krishpr0/CONTROLLEr/PICTURES/_PCB_v1_2026-Jun-18_11-57-01AM-000_CustomizedView5992248504-removebg-preview.png

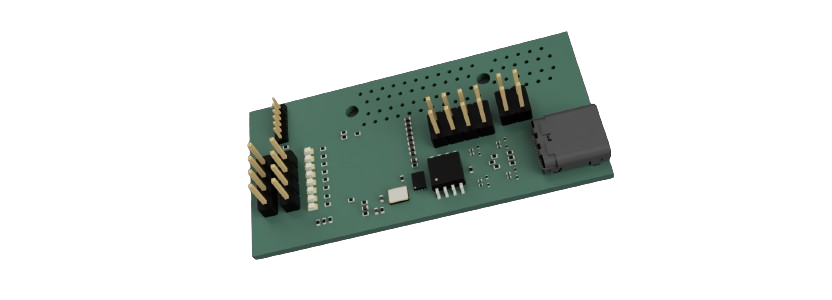
PICTURES/_PCB_v1_2026-Jun-18_11-57-01AM-000_CustomizedView5992248504-removebg-preview.png
