krishpr0/CONTROLLEr/PICTURES/_PCB_v1_2026-Jun-18_11-57-20AM-000_CustomizedView27303303591-removebg-preview.png

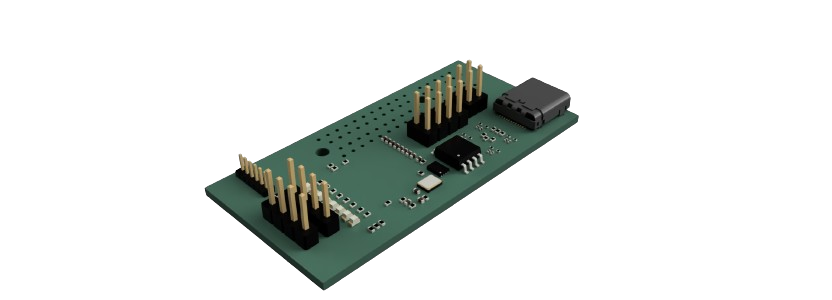
PICTURES/_PCB_v1_2026-Jun-18_11-57-20AM-000_CustomizedView27303303591-removebg-preview.png
