krishpr0/CONTROLLEr/PICTURES/_PCB_v54-removebg-preview.png

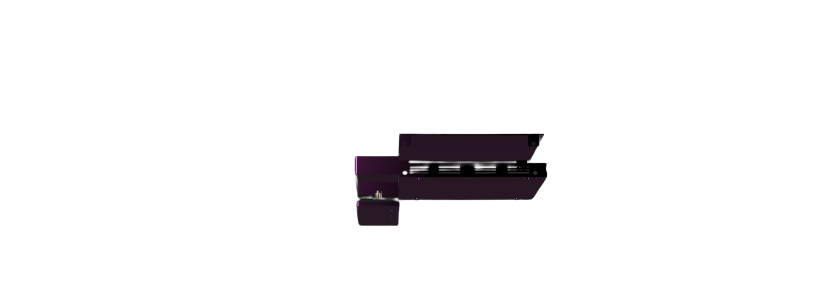
PICTURES/_PCB_v54-removebg-preview.png
