krishpr0/CONTROLLEr/PICTURES/CASE.png

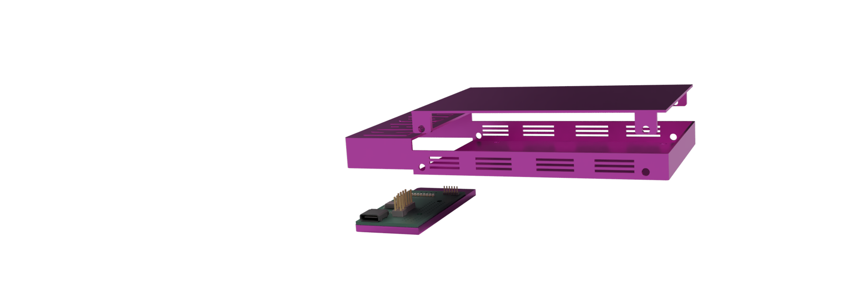
PICTURES/CASE.png
