krishpr0/CONTROLLEr/PICTURES/{PCB v46.png

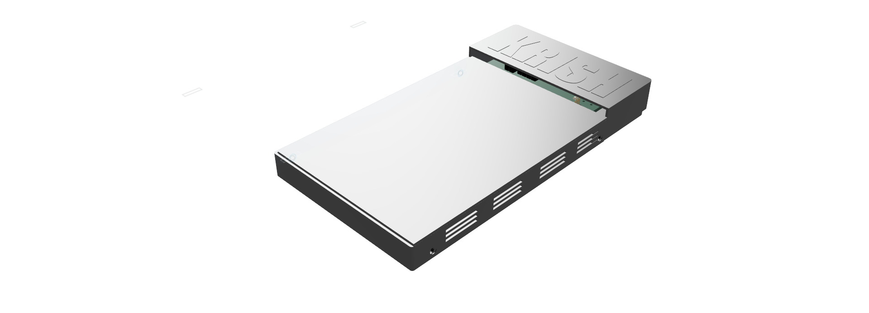
PICTURES/{PCB v46.png
