krishpr0/CONTROLLEr/PICTURES/{PCB v48.png

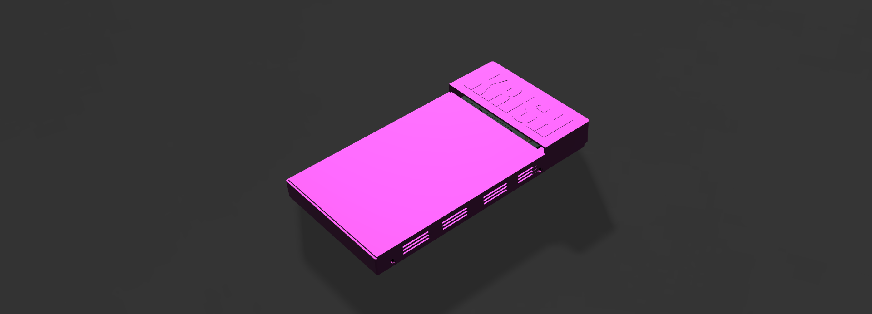
PICTURES/{PCB v48.png
