krishpr0/CONTROLLEr/PICTURES/{PCB v54.png

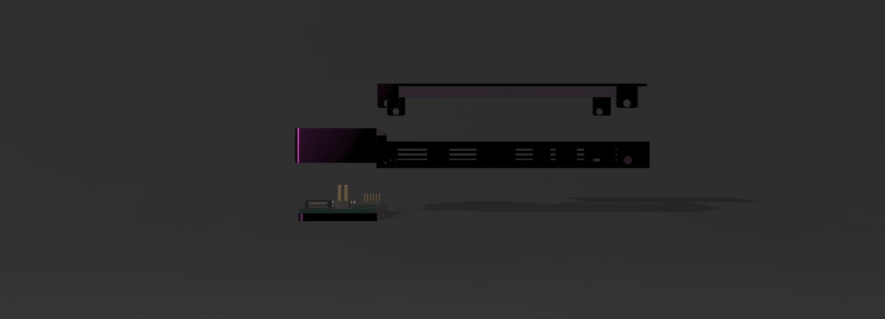
PICTURES/{PCB v54.png
