krishpr0/CONTROLLEr/PICTURES/{PCB_v1_2026-Jun-18_01-25-00PM-000_CustomizedView19356316654.png

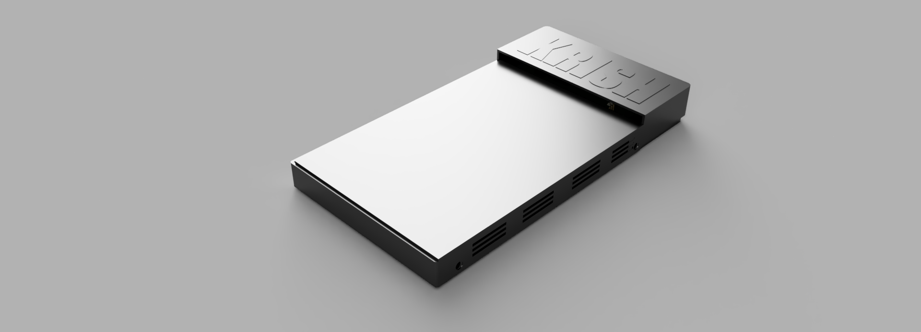
PICTURES/{PCB_v1_2026-Jun-18_01-25-00PM-000_CustomizedView19356316654.png
