krishpr0/CONTROLLEr/PICTURES/{PCB_v1_2026-Jun-18_04-54-52PM-000_CustomizedView25151271688.png

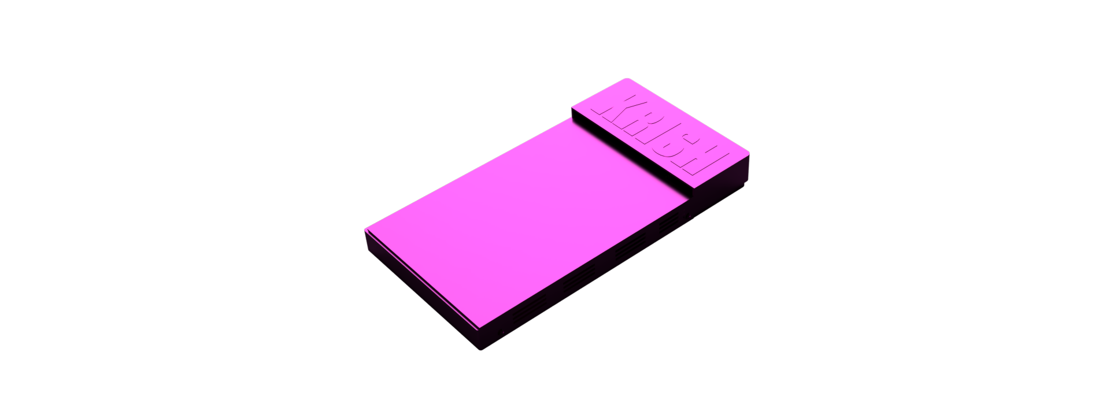
PICTURES/{PCB_v1_2026-Jun-18_04-54-52PM-000_CustomizedView25151271688.png
