krishpr0/CONTROLLEr/ZINE.png

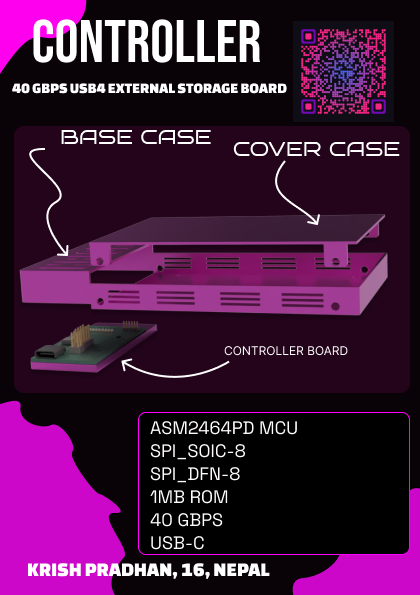
ZINE.png
