krishpr0/CONTROLLEr/FIRMWARE/src/src/app/buffer.c

/*
 * ASM2464PD Firmware - Buffer Controller Driver
 *
 * Handles buffer control, configuration, and data transfer management.
 * The buffer controller manages data movement between USB endpoints,
 * PCIe/NVMe, and internal memory.
 *
 *===========================================================================
 * BUFFER CONTROLLER ARCHITECTURE
 *===========================================================================
 *
 * Hardware Configuration:
 * - Internal data buffer for USB/PCIe transfers
 * - Configurable transfer modes and directions
 * - Status registers for tracking transfer progress
 *
 * Register Map (0xD800-0xD80F):
 * +-----------+----------------------------------------------------------+
 * | Address   | Description                                              |
 * +-----------+----------------------------------------------------------+
 * | 0xD800    | Buffer control (mode select: 0x03, 0x04)                 |
 * | 0xD801    | Buffer select                                            |
 * | 0xD802    | Buffer data/pointer                                      |
 * | 0xD803    | Pointer low                                              |
 * | 0xD804    | Pointer high / config from 0x911F                        |
 * | 0xD805    | Length low / config from 0x9120                          |
 * | 0xD806    | Status / config from 0x9121                              |
 * | 0xD807    | Length high / config from 0x9122                         |
 * | 0xD808    | Control global / params from idata[0x72]                 |
 * | 0xD809    | Threshold high / params from idata[0x71]                 |
 * | 0xD80A    | Threshold low / params from idata[0x70]                  |
 * | 0xD80B    | Flow control / params from idata[0x6f]                   |
 * | 0xD80C    | Transfer start (0x01=mode1, 0x02=mode2)                  |
 * +-----------+----------------------------------------------------------+
 *
 * Transfer Modes:
 * - Mode 0x03: Standard data transfer configuration
 * - Mode 0x04: Extended/special transfer configuration
 * - Transfer Start 0x01: Mode 1 transfer (USB/endpoint related)
 * - Transfer Start 0x02: Mode 2 transfer (PCIe/NVMe related)
 *
 * State Machine (idata[0x6a]):
 * - State 0x01: Idle/ready
 * - State 0x02: Transfer pending
 * - State 0x03: Transfer in progress
 * - State 0x04: Transfer complete
 * - State 0x05: Post-transfer processing
 * - State 0x08: Error/timeout
 *
 *===========================================================================
 * IMPLEMENTATION STATUS
 *===========================================================================
 * buf_set_ctrl_mode_4         [DONE] Set buffer to mode 0x04
 * buf_set_ctrl_mode_3         [DONE] Set buffer to mode 0x03
 * buf_write_idata_params      [DONE] Write idata params to buffer regs
 * buf_config_from_status      [DONE] Copy status regs to buffer config
 * buf_start_xfer_mode1        [DONE] Start mode 1 transfer
 * buf_start_xfer_mode2        [DONE] Start mode 2 transfer
 * buf_check_transfer_pending  [DONE] Check if transfer is pending
 *
 * Total: 7 functions implemented
 *===========================================================================
 */

#include "types.h"
#include "sfr.h"
#include "registers.h"
#include "globals.h"
#include "structs.h"

/*
 * buf_set_ctrl_mode_4 - Set buffer control to mode 0x04
 * Address: 0x025a-0x0269
 *
 * Configures the buffer for mode 0x04 operation and sets up
 * the length high register from xdata[0x0054].
 *
 * Original disassembly:
 *   025a: mov dptr, #0xd800   ; Buffer control
 *   025d: mov a, #0x04        ; Mode 4
 *   025f: movx @dptr, a       ; Write mode
 *   0260: mov dptr, #0x0054   ; Source address
 *   0263: movx a, @dptr       ; Read value
 *   0264: mov dptr, #0xd807   ; Length high
 *   0267: movx @dptr, a       ; Write length high
 *   0268: mov r4, #0x08       ; Return value in r4
 *   026a: sjmp 0x02c4         ; Continue...
 */
void buf_set_ctrl_mode_4(void)
{
    USB_BUF_CTRL->ctrl = 0x04;
    USB_BUF_CTRL->length_high = G_BUFFER_LENGTH_HIGH;
}

/*
 * buf_set_ctrl_mode_3 - Set buffer control to mode 0x03
 * Address: 0x026c-0x0271
 *
 * Configures the buffer for mode 0x03 operation.
 *
 * Original disassembly:
 *   026c: mov dptr, #0xd800   ; Buffer control
 *   026f: mov a, #0x03        ; Mode 3
 *   0271: movx @dptr, a       ; Write mode
 */
void buf_set_ctrl_mode_3(void)
{
    USB_BUF_CTRL->ctrl = 0x03;
}

/*
 * buf_write_idata_params - Write idata parameters to buffer registers
 * Address: 0x53c0-0x53d3
 *
 * Copies 4 bytes from idata[0x6f-0x72] to buffer registers 0xD808-0xD80B.
 * The bytes are written in reverse order (0x72->D808, 0x71->D809, etc).
 *
 * Original disassembly:
 *   53c0: mov r0, #0x72       ; Start at idata 0x72
 *   53c2: mov a, @r0          ; Read idata[0x72]
 *   53c3: mov dptr, #0xd808   ; Buffer control global
 *   53c6: movx @dptr, a       ; Write to D808
 *   53c7: dec r0              ; r0 = 0x71
 *   53c8: mov a, @r0          ; Read idata[0x71]
 *   53c9: inc dptr            ; dptr = 0xD809
 *   53ca: movx @dptr, a       ; Write to D809
 *   53cb: dec r0              ; r0 = 0x70
 *   53cc: mov a, @r0          ; Read idata[0x70]
 *   53cd: inc dptr            ; dptr = 0xD80A
 *   53ce: movx @dptr, a       ; Write to D80A
 *   53cf: dec r0              ; r0 = 0x6f
 *   53d0: mov a, @r0          ; Read idata[0x6f]
 *   53d1: inc dptr            ; dptr = 0xD80B
 *   53d2: movx @dptr, a       ; Write to D80B
 *   53d3: ret
 */
void buf_write_idata_params(void)
{
    /*
     * Note: This function uses idata (internal RAM) at addresses 0x6f-0x72.
     * In 8051, idata is accessed via indirect addressing with R0/R1.
     * These are internal state bytes for buffer configuration.
     */
    USB_BUF_CTRL->ctrl_global = I_BUF_CTRL_GLOBAL;   /* idata[0x72] -> 0xD808 */
    USB_BUF_CTRL->threshold_high = I_BUF_THRESH_HI;  /* idata[0x71] -> 0xD809 */
    USB_BUF_CTRL->threshold_low = I_BUF_THRESH_LO;   /* idata[0x70] -> 0xD80A */
    USB_BUF_CTRL->flow_ctrl = I_BUF_FLOW_CTRL;       /* idata[0x6f] -> 0xD80B */
}

/*
 * buf_config_from_status - Configure buffer from status registers
 * Address: 0x3147-0x3167
 *
 * Copies configuration from status registers 0x911F-0x9122 to
 * buffer registers 0xD804-0xD807.
 *
 * Original disassembly:
 *   3147: mov dptr, #0x911f   ; Status source
 *   314a: movx a, @dptr       ; Read 0x911F
 *   314b: mov dptr, #0xd804   ; Buffer ptr high
 *   314e: movx @dptr, a       ; Write to D804
 *   314f: mov dptr, #0x9120   ; Status source
 *   3152: movx a, @dptr       ; Read 0x9120
 *   3153: mov dptr, #0xd805   ; Buffer length low
 *   3156: movx @dptr, a       ; Write to D805
 *   3157: mov dptr, #0x9121   ; Status source
 *   315a: movx a, @dptr       ; Read 0x9121
 *   315b: mov dptr, #0xd806   ; Buffer status
 *   315e: movx @dptr, a       ; Write to D806
 *   315f: mov dptr, #0x9122   ; Status source
 *   3162: movx a, @dptr       ; Read 0x9122
 *   3163: mov dptr, #0xd807   ; Buffer length high
 *   3166: movx @dptr, a       ; Write to D807
 *   3167: ret
 */
void buf_config_from_status(void)
{
    USB_BUF_CTRL->ptr_high = REG_CBW_TAG_0;
    USB_BUF_CTRL->length_low = REG_CBW_TAG_1;
    USB_BUF_CTRL->status = REG_CBW_TAG_2;
    USB_BUF_CTRL->length_high = REG_CBW_TAG_3;
}

/*
 * buf_start_xfer_mode1 - Start buffer transfer in mode 1
 * Address: 0x5256-0x525f
 *
 * Initiates a mode 1 buffer transfer by writing 0x01 to the
 * transfer start register, then calls the transfer handler.
 *
 * Original disassembly:
 *   5256: mov dptr, #0xd80c   ; Transfer start reg
 *   5259: mov a, #0x01        ; Mode 1
 *   525b: movx @dptr, a       ; Start transfer
 *   525c: lcall 0x1bcb        ; Call transfer handler
 *   525f: ret
 */
void buf_start_xfer_mode1(void)
{
    USB_BUF_CTRL->xfer_start = 0x01;
    /* Note: Original calls 0x1bcb which is a transfer handler
     * that processes the buffer state machine. The actual
     * transfer handler would need to be called here. */
}

/*
 * buf_start_xfer_mode2 - Start buffer transfer in mode 2
 * Address: 0x018b-0x0198
 *
 * Initiates a mode 2 buffer transfer by writing 0x02 to the
 * transfer start register, calls the transfer handler, and
 * sets the state machine to state 0x05.
 *
 * Original disassembly:
 *   018b: mov dptr, #0xd80c   ; Transfer start reg
 *   018e: mov a, #0x02        ; Mode 2
 *   0190: movx @dptr, a       ; Start transfer
 *   0191: lcall 0x01ea        ; Call helper (writes idata params)
 *   0194: mov r0, #0x6a       ; State variable address
 *   0196: mov @r0, #0x05      ; Set state to 5
 *   0198: ret
 */
void buf_start_xfer_mode2(void)
{
    __idata uint8_t *state_ptr = (__idata uint8_t *)0x6a;

    USB_BUF_CTRL->xfer_start = 0x02;
    /* Note: Original calls 0x01ea which calls buf_write_idata_params
     * and then sets a register. For now we just set the state. */
    buf_write_idata_params();
    *state_ptr = 0x05;
}

/*
 * buf_check_transfer_pending - Check if a transfer operation is pending
 * Address: 0x313d-0x3146
 *
 * Reads 4 bytes from idata[0x6b-0x6e] and returns non-zero if any
 * are set, indicating a pending transfer operation.
 *
 * Original disassembly:
 *   313d: mov r0, #0x6b       ; Start address
 *   313f: lcall 0x0d78        ; Read 4 bytes into r4-r7
 *   3142: mov a, r4           ; Check r4
 *   3143: orl a, r5           ; OR with r5
 *   3144: orl a, r6           ; OR with r6
 *   3145: orl a, r7           ; OR with r7
 *   3146: ret                 ; Return non-zero if any set
 */
uint8_t buf_check_transfer_pending(void)
{
    __idata uint8_t *ptr = (__idata uint8_t *)0x6b;
    uint8_t result;

    result = ptr[0];
    result |= ptr[1];
    result |= ptr[2];
    result |= ptr[3];

    return result;
}


/* ============================================================
 * Buffer Address Calculation Functions
 * ============================================================ */

/*
 * FUN_CODE_5043 - Calculate buffer address with 0x08 offset and read
 * Address: 0x5043-0x504e (12 bytes)
 *
 * Disassembly:
 *   5043: mov a, #0x08
 *   5045: add a, r7          ; A = 0x08 + R7
 *   5046: mov 0x82, a        ; DPL = result
 *   5048: clr a
 *   5049: addc a, #0x01      ; DPH = 0x01 + carry
 *   504b: mov 0x83, a
 *   504d: movx a, @dptr      ; Read byte
 *   504e: ret
 *
 * Returns: XDATA[0x0108 + R7]
 */
uint8_t buf_read_offset_08(uint8_t param)
{
    uint16_t addr = 0x0108 + param;
    return XDATA_REG8(addr);
}

/*
 * buf_read_base - Alternate entry into buf_read_offset_08 (at mov DPL instruction)
 * Address: 0x5046-0x504e (9 bytes)
 *
 * From ghidra.c: return *(undefined1 *)CONCAT11('\x01' - (in_PSW >> 7), param_1)
 * Reads from address (0x01xx or 0x00xx based on carry) + param
 */
uint8_t buf_read_base(uint8_t param)
{
    /* Read from 0x0100 + param (assuming no carry from prior add) */
    return G_USB_BUF_BASE[param];
}

/*
 * buf_read_offset_3e - Read from calculated address (param - 0x3E)
 * Address: 0x505d-0x5066 (10 bytes)
 *
 * From ghidra.c: return *(undefined1 *)CONCAT11(-(((0x3d < param_1) << 7) >> 7), param_1 - 0x3e)
 * Reads from address calculated as (high_byte, param - 0x3E)
 * High byte is 0xFF if param <= 0x3D (borrow), else 0x00
 */
uint8_t buf_read_offset_3e(uint8_t param)
{
    uint16_t addr;
    if (param <= 0x3D) {
        addr = 0xFF00 + (uint8_t)(param - 0x3E);  /* Borrow case */
    } else {
        addr = (uint8_t)(param - 0x3E);  /* Normal case */
    }
    return XDATA8(addr);
}
